TDA-2030/PulseMeter/firmware/main/app_main.cpp

#include <string.h>
#include "freertos/FreeRTOS.h"
#include "freertos/task.h"
#include "esp_log.h"
#include "nvs_flash.h"
#include "helper.h"
#include "setting.h"
#include "wifi.h"
#include "led.h"
#include "board.h"
#include "firmware_version.h"
#include "meter_dial.h"
#include "meter_server.h"

static const char *TAG = "app_main";

MeterDial meters[] = {
    MeterDial("Meter1"),
    MeterDial("Meter2"),
};
led_handle_t meter_leds[] = { nullptr, nullptr };

MeterServer server;

extern "C" void app_main()
{
    ESP_LOGI(TAG, "Starting PulseMeter firmware v%s", FIRMWARE_VERSION_STRING);

    /* Initialize NVS. */
    esp_err_t err = nvs_flash_init();
    if (err == ESP_ERR_NVS_NO_FREE_PAGES || err == ESP_ERR_NVS_NEW_VERSION_FOUND) {
        ESP_ERROR_CHECK(nvs_flash_erase());
        err = nvs_flash_init();
    }
    ESP_ERROR_CHECK( err );

    g_settings.load();
    vTaskDelay(pdMS_TO_TICKS(100));
    board_init();
    ESP_ERROR_CHECK(led_create(BOARD_IO_LED_STRIP1, 16, 0, &meter_leds[0]));
    ESP_ERROR_CHECK(led_create(BOARD_IO_LED_STRIP2, 16, 0, &meter_leds[1]));
    ESP_ERROR_CHECK(led_set_pixel(meter_leds[0], 255, 255, 255));
    ESP_ERROR_CHECK(led_set_pixel(meter_leds[1], 255, 255, 255));
    ESP_ERROR_CHECK(led_refresh(meter_leds[0]));
    ESP_ERROR_CHECK(led_refresh(meter_leds[1]));

    /** Determine whether to restore the settings by reading the restart count */
    int restart_cnt = restart_count_get();
    ESP_LOGI(TAG, "Restart count=[%d]", restart_cnt);
    if (restart_cnt >= RESTART_COUNT_RESET) {
        ESP_LOGW(TAG, "Erase information saved in flash and restart");
        ESP_ERROR_CHECK(nvs_flash_erase());
    }
    meters[0].init(BOARD_IO_METER1);
    meters[1].init(BOARD_IO_METER2);

    // Load calibrated duty ceilings from NVS (defaults: 448 / 236)
    meters[0].set_max_duty(g_settings.meter1_max_duty);
    meters[1].set_max_duty(g_settings.meter2_max_duty);

    meters[0].waitSelfTestDone();
    meters[1].waitSelfTestDone();

    start_wifi();
    server.startServer();
}
