TDA-2030/PulseMeter/firmware/main/helper.c

#include <time.h>
#include <sys/time.h>
#include <string.h>
#include "freertos/FreeRTOS.h"
#include "freertos/task.h"
#include "freertos/timers.h"
#include "esp_log.h"
#include "nvs.h"
#include "esp_rom_sys.h"
#include "helper.h"

static const char *TAG = "helper";

#define HELPER_CHECK_GT(a, str, label) \
    if (!(a)) { \
        ESP_LOGE(TAG,"%s(%d): %s", __FUNCTION__, __LINE__, str); \
        goto label; \
    }

#define HELPER_CHECK(a, str, ret) \
    if (!(a)) { \
        ESP_LOGE(TAG,"%s(%d): %s", __FUNCTION__, __LINE__, str); \
        return ret; \
    }

esp_err_t iot_param_save(const char *space_name, const char *key, void *param, uint16_t len)
{
    esp_err_t ret = ESP_ERR_INVALID_ARG;
    HELPER_CHECK_GT(NULL != space_name, "Pointer of space_name is invalid", OPEN_FAIL);
    HELPER_CHECK_GT(NULL != key, "Pointer of key is invalid", OPEN_FAIL);
    HELPER_CHECK_GT(NULL != param, "Pointer of param is invalid", OPEN_FAIL);
    nvs_handle_t my_handle;
    ret = nvs_open(space_name, NVS_READWRITE, &my_handle);
    HELPER_CHECK_GT(ESP_OK == ret, "nvs open failed", OPEN_FAIL);
    ret = nvs_set_blob(my_handle, key, param, len);
    HELPER_CHECK_GT(ESP_OK == ret, "nvs set blob failed", SAVE_FINISH);
    ret = nvs_commit(my_handle);

SAVE_FINISH:
    nvs_close(my_handle);

OPEN_FAIL:
    return ret;
}

esp_err_t iot_param_load(const char *space_name, const char *key, void *dest)
{
    esp_err_t ret = ESP_ERR_INVALID_ARG;
    HELPER_CHECK_GT(NULL != space_name, "Pointer of space_name is invalid", OPEN_FAIL);
    HELPER_CHECK_GT(NULL != key, "Pointer of key is invalid", OPEN_FAIL);
    HELPER_CHECK_GT(NULL != dest, "Pointer of dest is invalid", OPEN_FAIL);
    nvs_handle_t my_handle;
    size_t required_size = 0;
    ret = nvs_open(space_name, NVS_READWRITE, &my_handle);
    HELPER_CHECK_GT(ESP_OK == ret, "nvs open failed", OPEN_FAIL);
    ret = nvs_get_blob(my_handle, key, NULL, &required_size);
    HELPER_CHECK_GT(ESP_OK == ret, "nvs get blob failed", LOAD_FINISH);
    if (required_size == 0) {
        ESP_LOGW(TAG, "the target you want to load has never been saved");
        ret = ESP_FAIL;
        goto LOAD_FINISH;
    }
    ret = nvs_get_blob(my_handle, key, dest, &required_size);

LOAD_FINISH:
    nvs_close(my_handle);

OPEN_FAIL:
    return ret;
}

esp_err_t iot_param_erase(const char *space_name, const char *key)
{
    esp_err_t ret = ESP_ERR_INVALID_ARG;
    HELPER_CHECK_GT(NULL != space_name, "Pointer of space_name is invalid", OPEN_FAIL);
    HELPER_CHECK_GT(NULL != key, "Pointer of key is invalid", OPEN_FAIL);
    nvs_handle_t my_handle;
    ret = nvs_open(space_name, NVS_READWRITE, &my_handle);
    HELPER_CHECK_GT(ESP_OK == ret, "nvs open failed", OPEN_FAIL);
    ret = nvs_erase_key(my_handle, key);
    HELPER_CHECK_GT(ESP_OK == ret, "nvs erase failed", ERASE_FINISH);
    ret = nvs_commit(my_handle);

ERASE_FINISH:
    nvs_close(my_handle);

OPEN_FAIL:
    return ret;
}


#define DEVICE_RESTART_TIMEOUT_MS                   (3000)
#define DEVICE_STORE_RESTART_COUNT_NAME_SPACE       "RestartCntName"
#define DEVICE_STORE_RESTART_COUNT_KEY              "RestartCount"

static void restart_count_erase_timercb(TimerHandle_t timer)
{
    if (!xTimerStop(timer, portMAX_DELAY)) {
        ESP_LOGE(TAG, "xTimerStop timer: %p", timer);
    }

    if (!xTimerDelete(timer, portMAX_DELAY)) {
        ESP_LOGE(TAG, "xTimerDelete timer: %p", timer);
    }

    uint32_t restart_count = 1;
    iot_param_save(DEVICE_STORE_RESTART_COUNT_NAME_SPACE, DEVICE_STORE_RESTART_COUNT_KEY, &restart_count, sizeof(uint32_t));
    ESP_LOGD(TAG, "Reset restart count");
}

int restart_count_get()
{
    esp_err_t ret              = ESP_OK;
    static TimerHandle_t timer = NULL;
    uint32_t restart_count     = 0;
    soc_reset_reason_t reset_reason  = esp_rom_get_reset_reason(0);
    ret = iot_param_load(DEVICE_STORE_RESTART_COUNT_NAME_SPACE, DEVICE_STORE_RESTART_COUNT_KEY, &restart_count);

    ESP_LOGW(TAG, "restart reason: %u", reset_reason);
    if (timer) {
        return restart_count;
    }

    /**< If the device restarts within the instruction time,
         the event_mdoe value will be incremented by one */
    if (reset_reason == RESET_REASON_CHIP_POWER_ON || reset_reason == RESET_REASON_CORE_RTC_WDT) {
        restart_count++;
        ESP_LOGD(TAG, "restart count: %u", restart_count);
    } else {
        restart_count = 1;
    }

    ret = iot_param_save(DEVICE_STORE_RESTART_COUNT_NAME_SPACE, DEVICE_STORE_RESTART_COUNT_KEY, &restart_count, sizeof(uint32_t));
    HELPER_CHECK(ret == ESP_OK, "Save the number of restarts failed", restart_count);

    timer = xTimerCreate("restart_count_erase", DEVICE_RESTART_TIMEOUT_MS / portTICK_PERIOD_MS,
                         false, NULL, restart_count_erase_timercb);
    HELPER_CHECK(NULL != timer, "xTimerCreate failed", restart_count);

    xTimerStart(timer, 0);

    return restart_count;
}

void set_time(int year, int month, int day, int hour, int min, int sec, bool is_utc)
{
    struct tm timeinfo = {0};
    timeinfo.tm_year = year - 1900;
    timeinfo.tm_mon = month - 1;
    timeinfo.tm_mday = day;
    timeinfo.tm_hour = hour;
    timeinfo.tm_min = min;
    timeinfo.tm_sec = sec;
    if (is_utc) {
        setenv("TZ", "UTC+0", 1);
    } else {
        setenv("TZ", "CST-8", 1);
    }
    tzset(); // Set timezone
    time_t timeSinceEpoch = mktime(&timeinfo);
    struct timeval now = { .tv_sec = timeSinceEpoch };
    settimeofday(&now, NULL);

    // reconfig timezone
    setenv("TZ", "CST-8", 1);
    tzset();
}
